MediaLabUniovi/Sensor-Cooper/pics/4_Martin Cooper y Arlene Harris.jpg

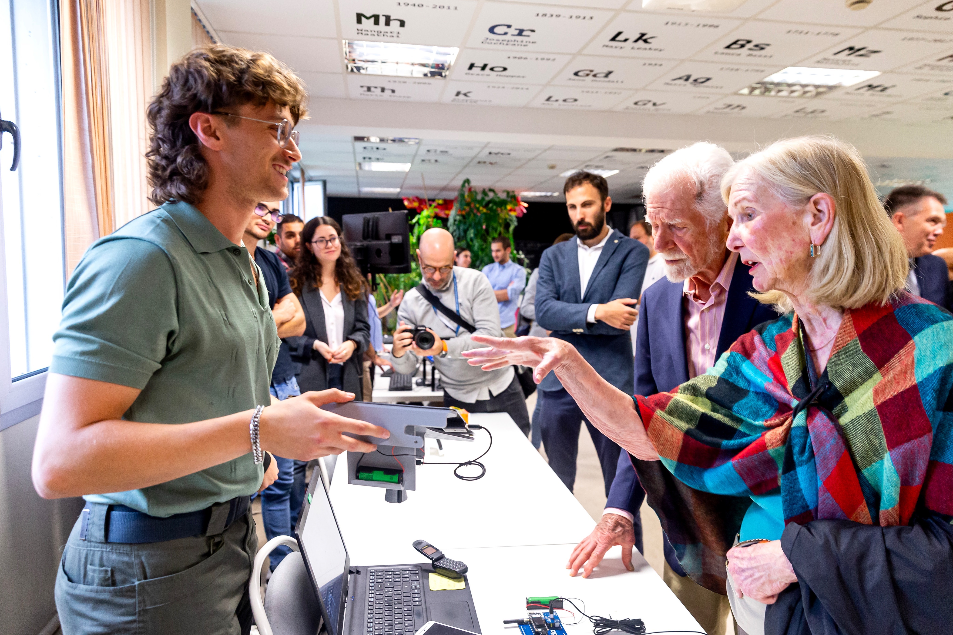
pics/4_Martin Cooper y Arlene Harris.jpg
