MediaLabUniovi/Sensor-Cooper/pics/5_Carcasa + Electrónica montada.jpg

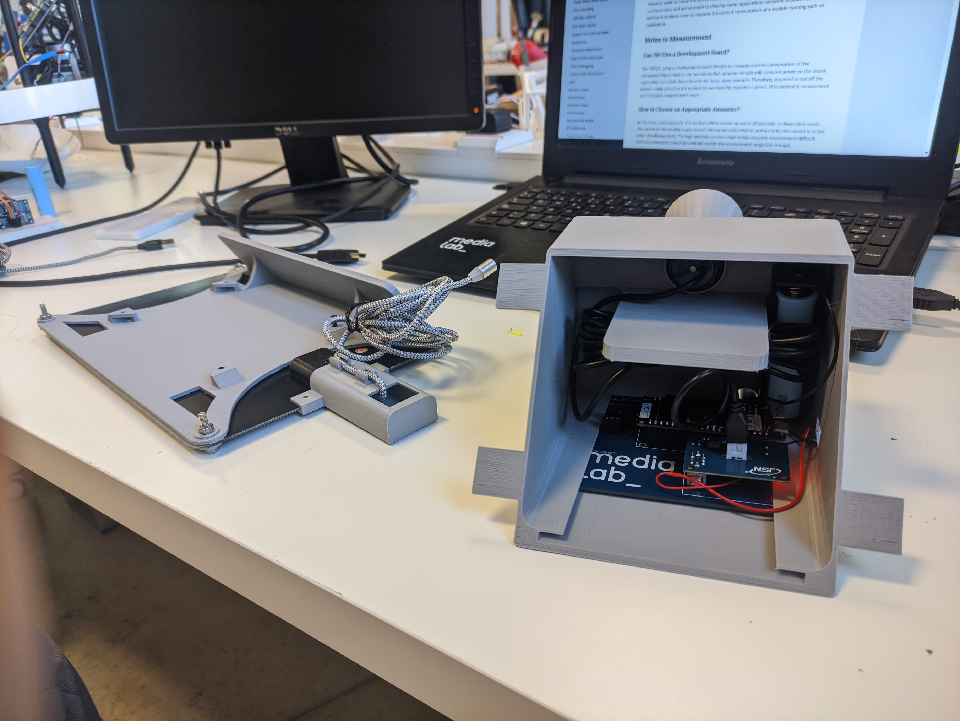
pics/5_Carcasa + Electrónica montada.jpg
