MediaLabUniovi/Sensor-Cooper/pics/escuela-politecnica-ingenieria (4).jpg

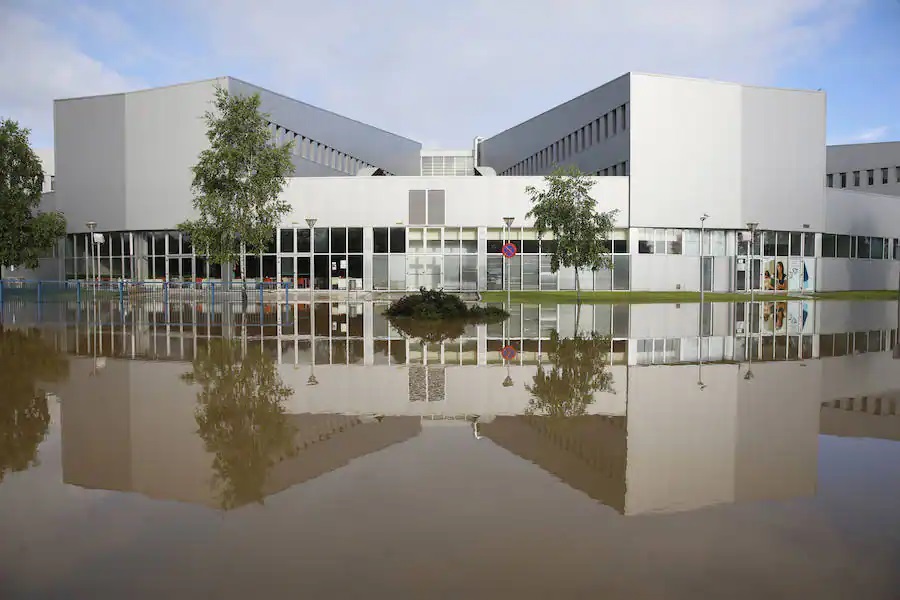
pics/escuela-politecnica-ingenieria (4).jpg
