MediaLabUniovi/Sensor-Cooper/pics/escuela-politecnica-ingenieria (12).jpg

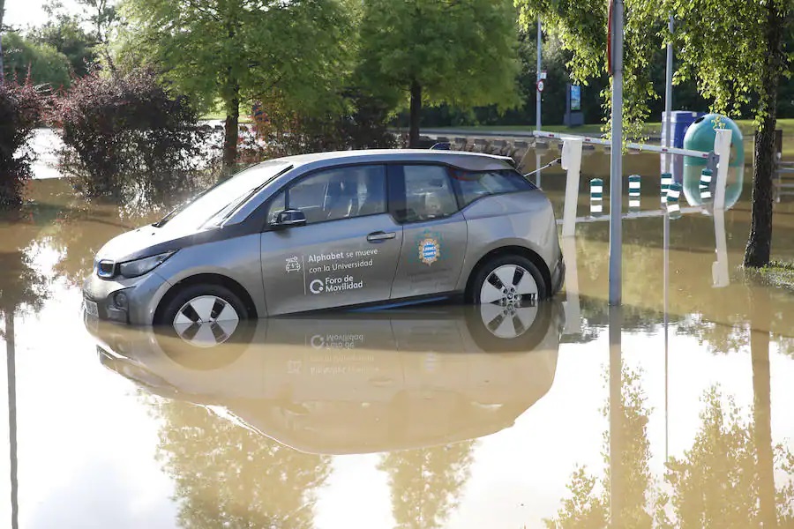
pics/escuela-politecnica-ingenieria (12).jpg
