MediaLabUniovi/Sensor-Cooper/pics/Screenshot 2023-11-13 194151.png

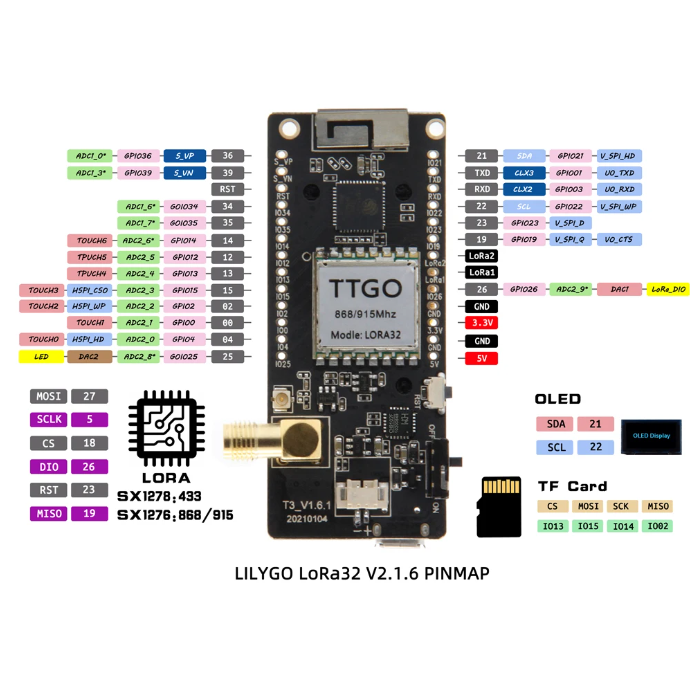
pics/Screenshot 2023-11-13 194151.png
