MediaLabUniovi/Sensor-Cooper/pics/Screenshot 2023-11-30 182339.png

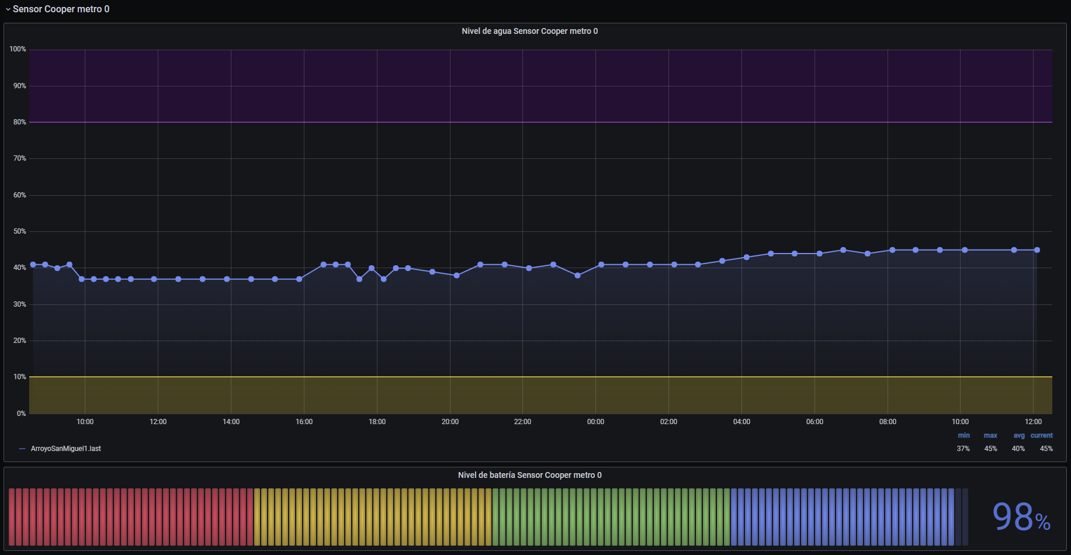
pics/Screenshot 2023-11-30 182339.png
