MediaLabUniovi/Sensor-Cooper/pics/Screenshot 2023-12-01 175741.png

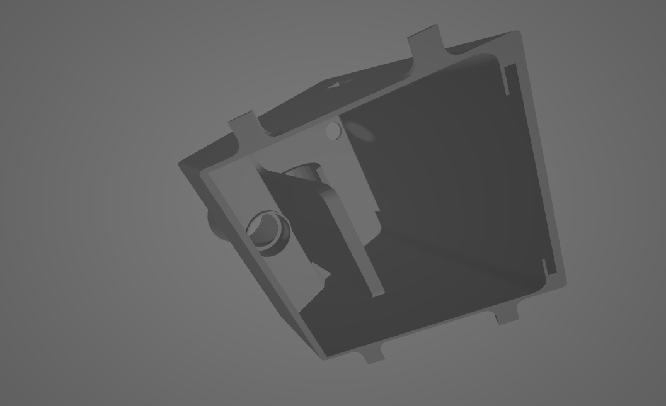
pics/Screenshot 2023-12-01 175741.png
