MediaLabUniovi/Sensor-Cooper/pics/Screenshot 2023-12-04 113305.png

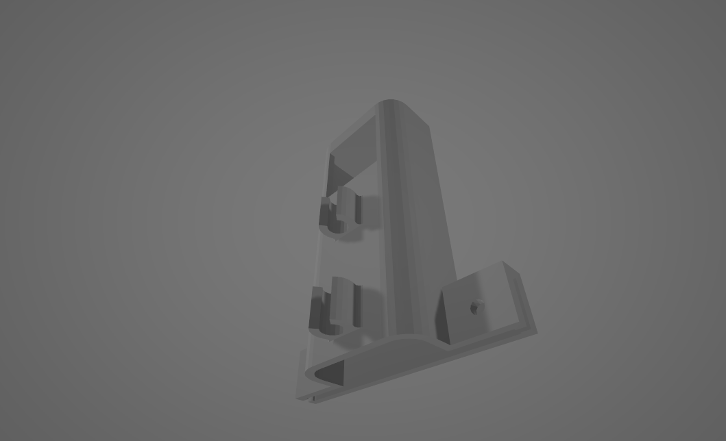
pics/Screenshot 2023-12-04 113305.png
