MediaLabUniovi/Sensor-Cooper/pics/Screenshot 2024-01-22 172558.png

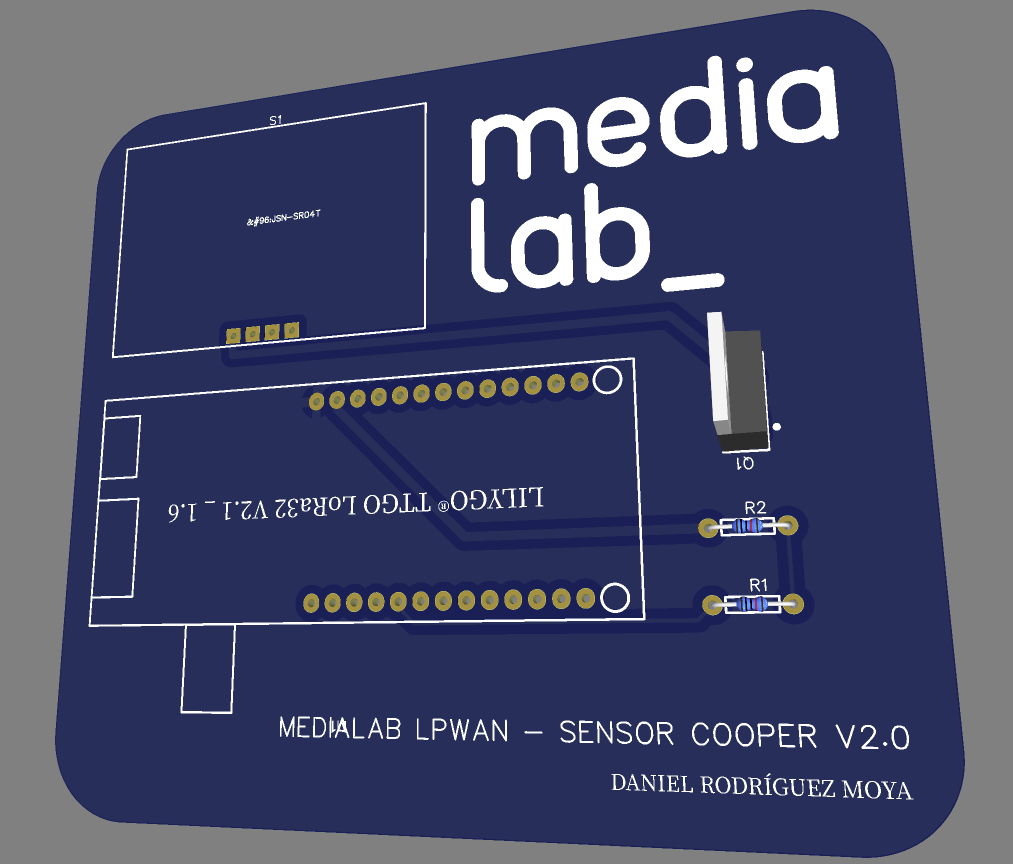
pics/Screenshot 2024-01-22 172558.png
